tmhmitchell/K02/other/img/photos/img (0).jpg

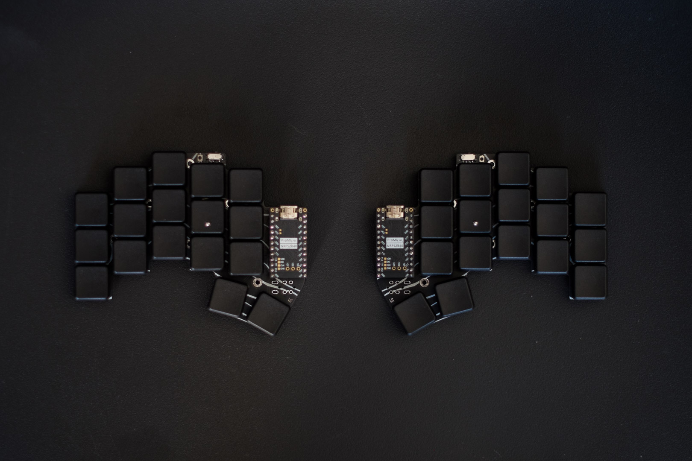
other/img/photos/img (0).jpg
