tmhmitchell/K02/other/img/photos/img (2).jpg

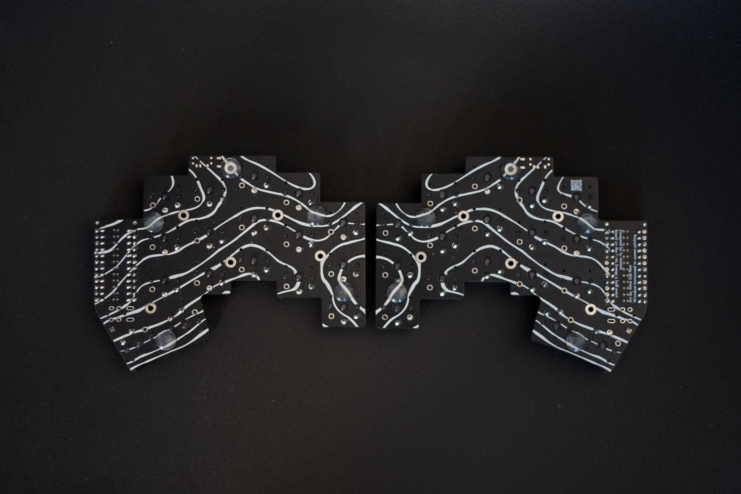
other/img/photos/img (2).jpg
