tmhmitchell/K02/other/img/photos/img (4).jpg

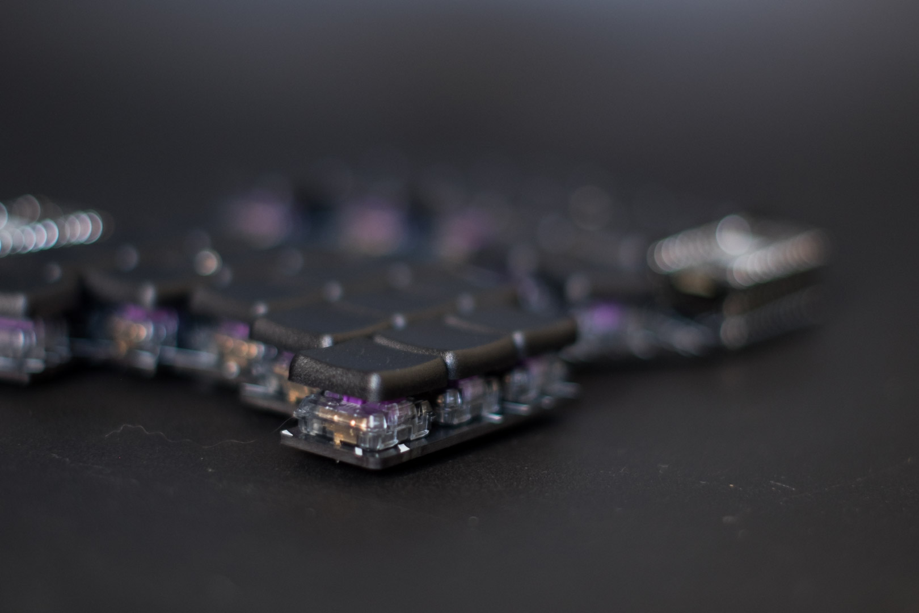
other/img/photos/img (4).jpg
