tmhmitchell/K02/other/img/photos/img (9).jpg

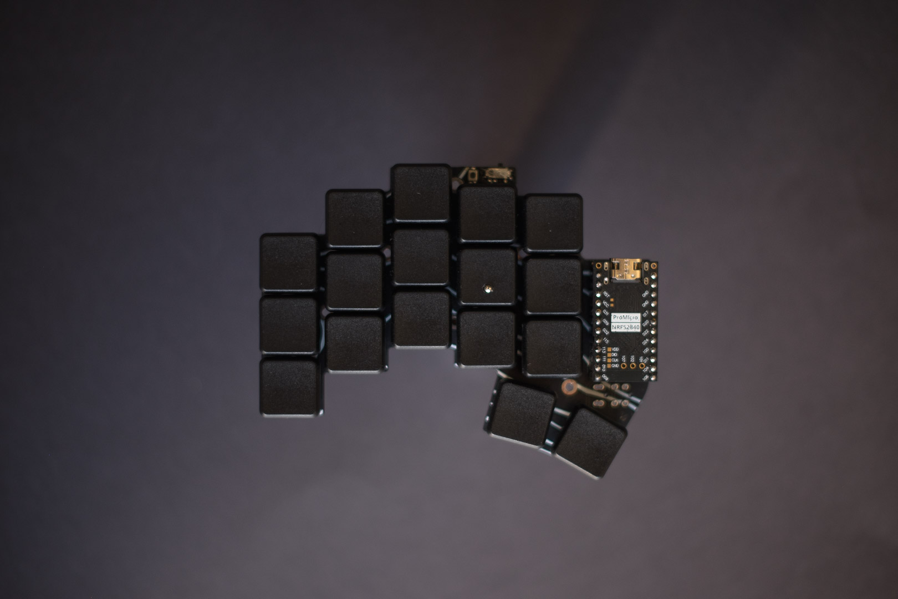
other/img/photos/img (9).jpg
