tmhmitchell/K02/other/img/photos/img (10).jpg

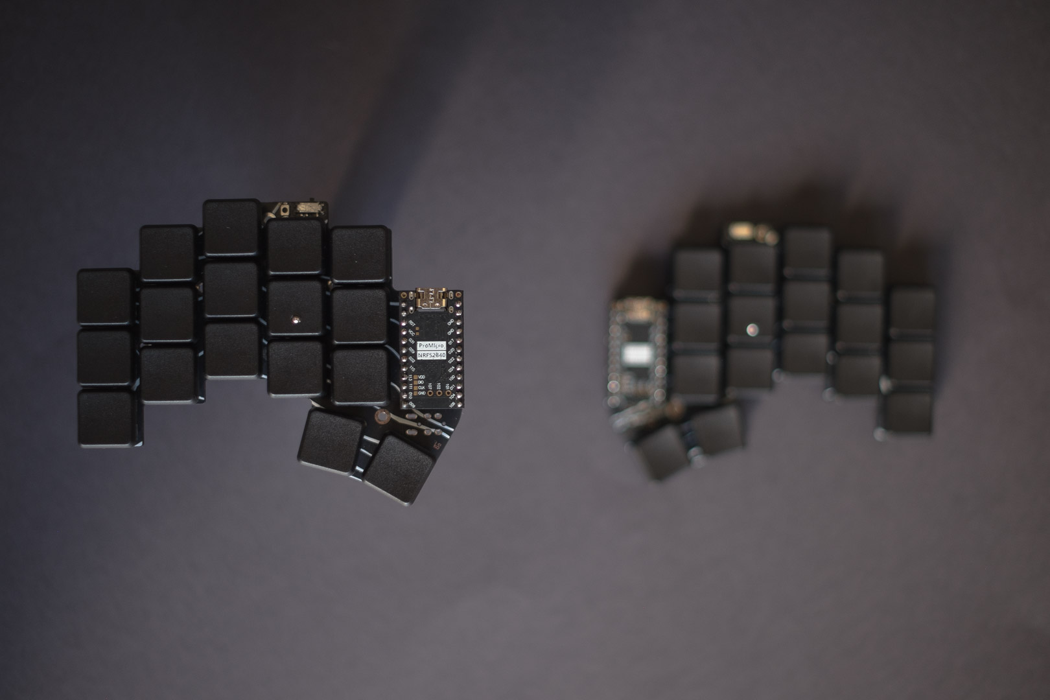
other/img/photos/img (10).jpg
