tmhmitchell/K02/other/img/photos/img (11).jpg

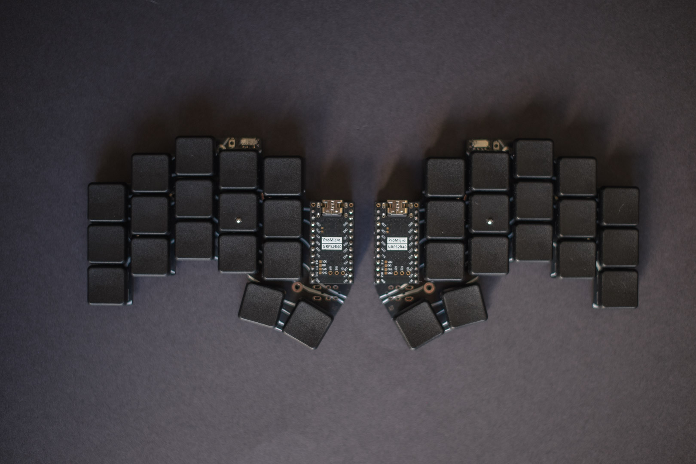
other/img/photos/img (11).jpg
