tmhmitchell/K02/other/img/photos/img (12).jpg

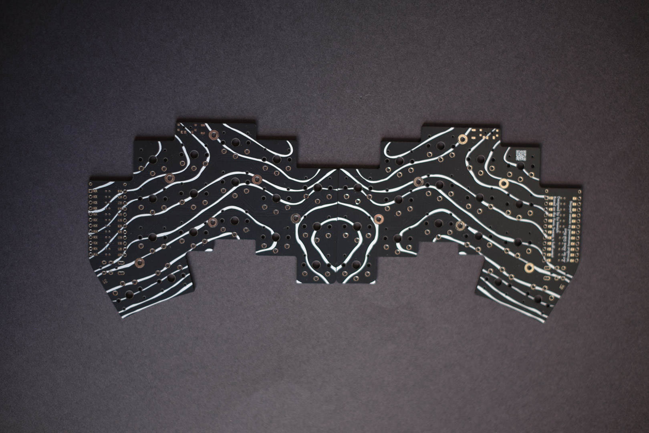
other/img/photos/img (12).jpg
