tmhmitchell/K02/other/img/photos/img (13).jpg

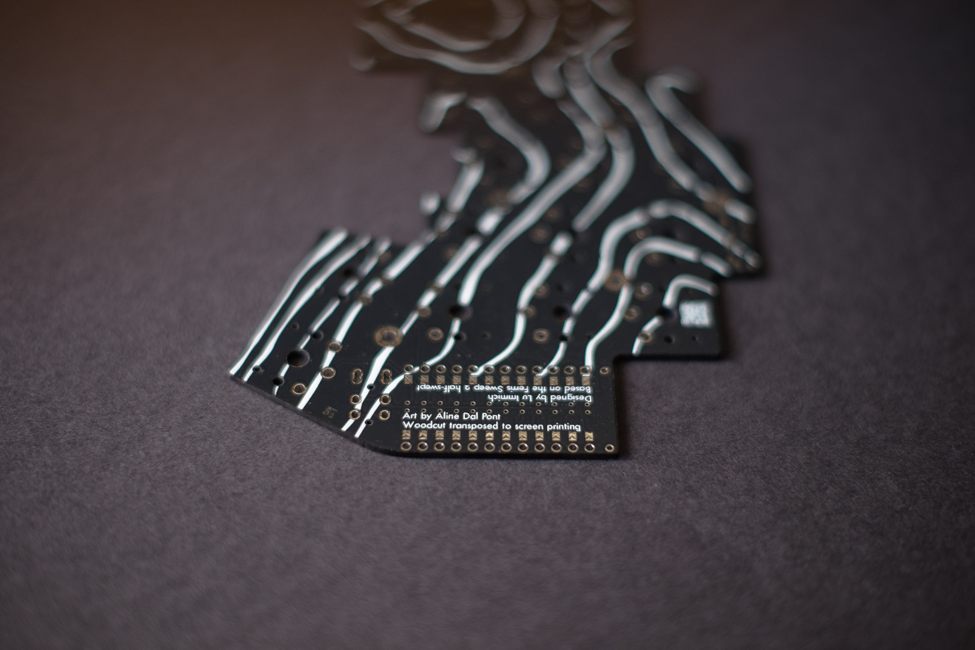
other/img/photos/img (13).jpg
