tmhmitchell/K02/other/img/photos/img (14).jpg

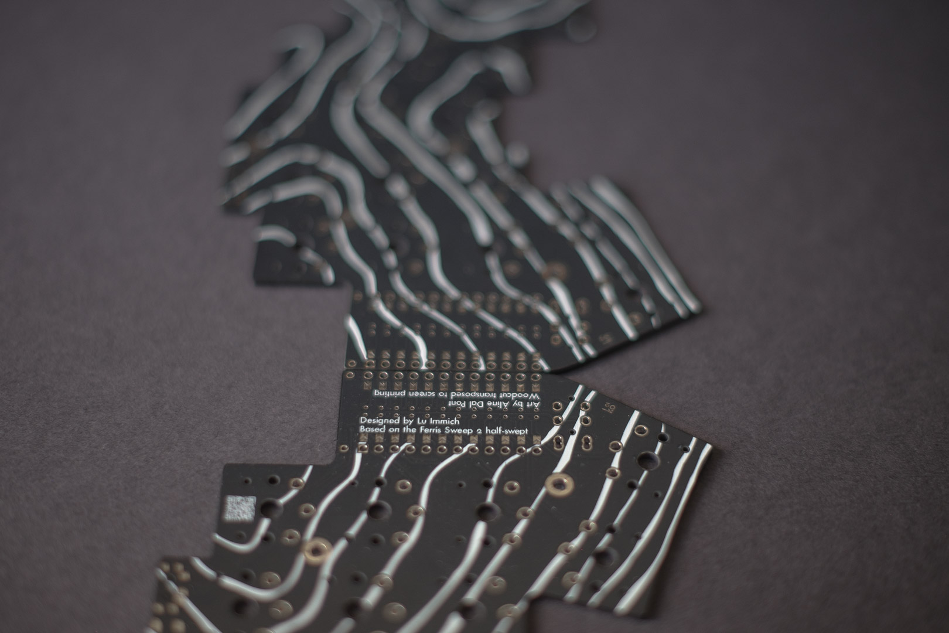
other/img/photos/img (14).jpg
