tmhmitchell/K02/other/img/photos/img (15).jpg

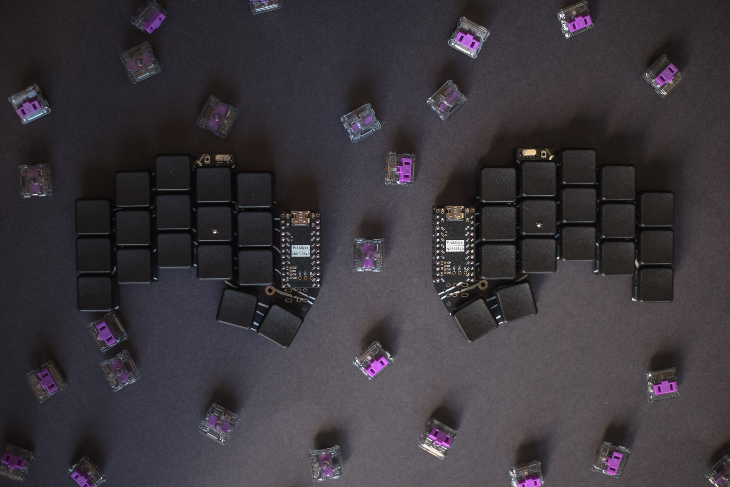
other/img/photos/img (15).jpg
