tmhmitchell/K02/other/img/photos/img (16).jpg

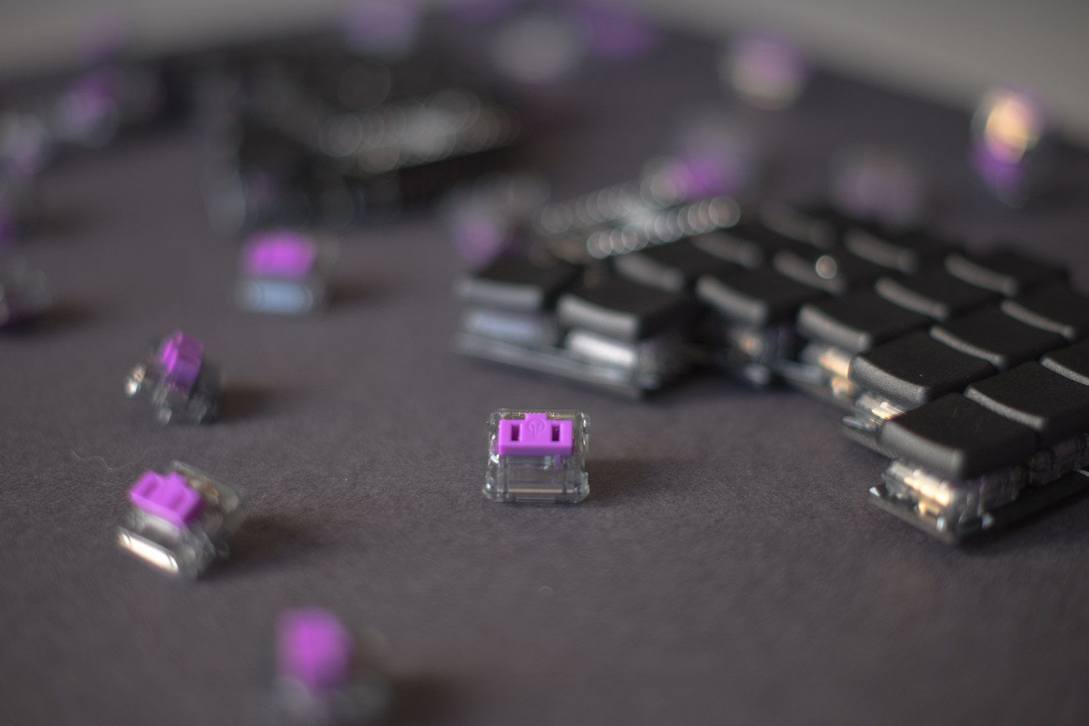
other/img/photos/img (16).jpg
