tmhmitchell/K02/other/img/photos/img (17).jpg

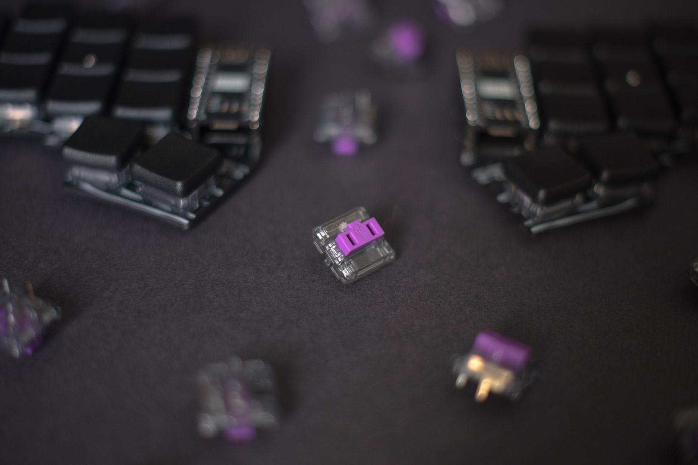
other/img/photos/img (17).jpg
